mikhailrussell/LAS-Laboratory-Access-System/data/ESP-Now_2_0.01.jpg

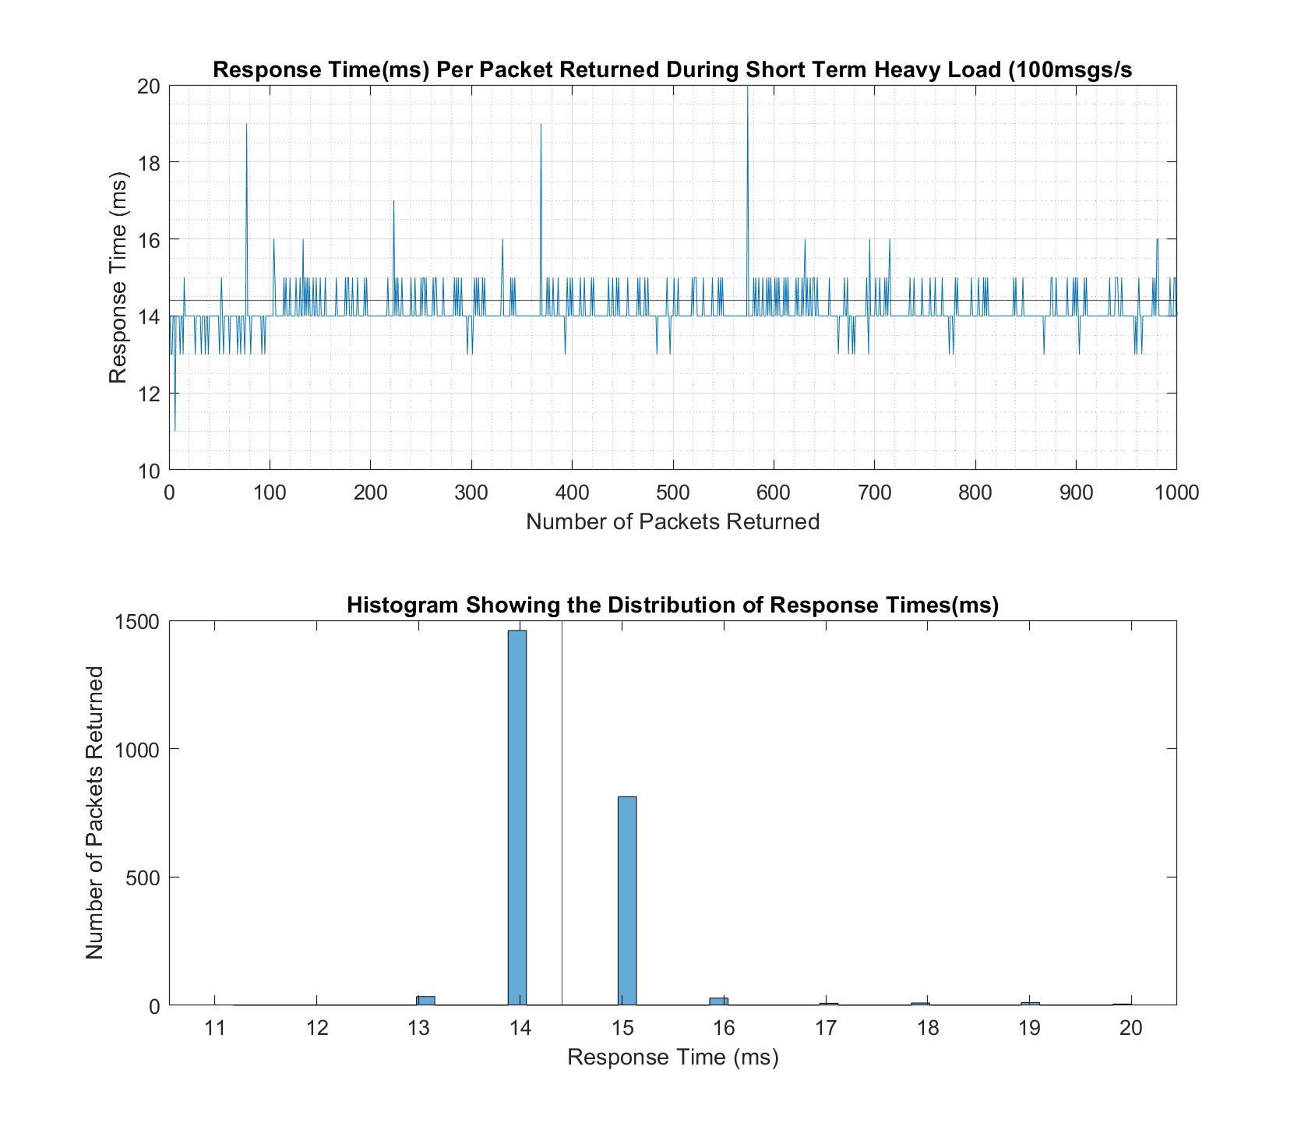
data/ESP-Now_2_0.01.jpg
