mikhailrussell/LAS-Laboratory-Access-System/data/Zero-Crossing_anaylsis/Crossing_image_1.jpg

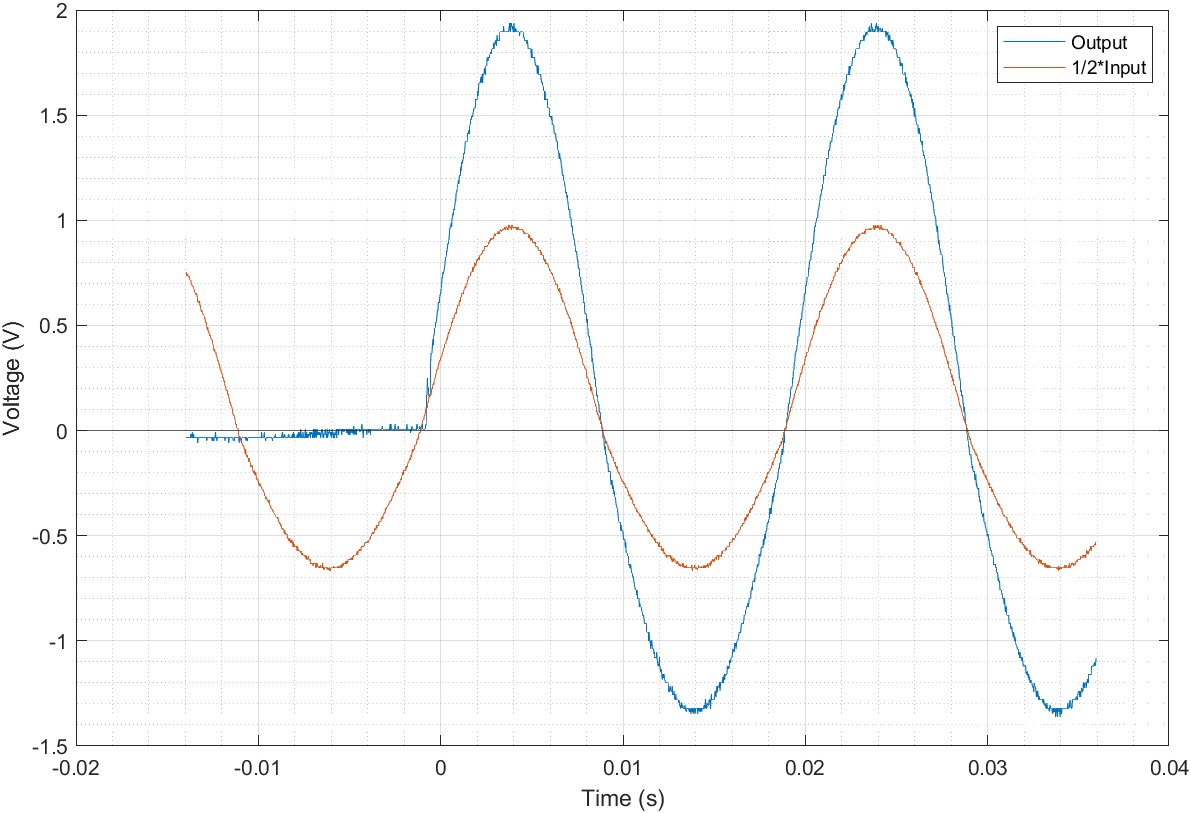
data/Zero-Crossing_anaylsis/Crossing_image_1.jpg
