mikhailrussell/LAS-Laboratory-Access-System/sim/plots/res_sim.png

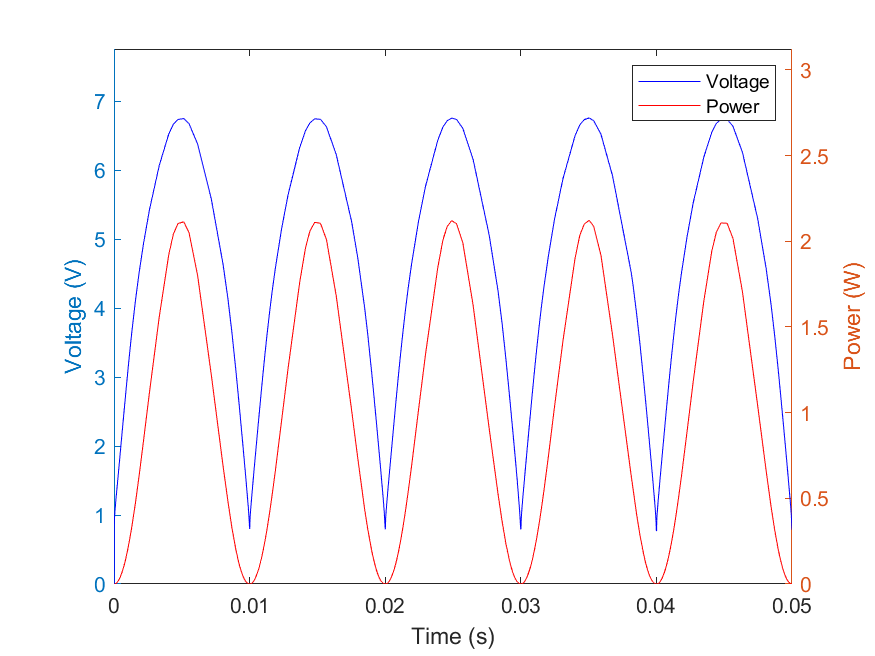
sim/plots/res_sim.png
