mikhailrussell/LAS-Laboratory-Access-System/data/Zero-Crossing_anaylsis/zero_crossing_results.jpg

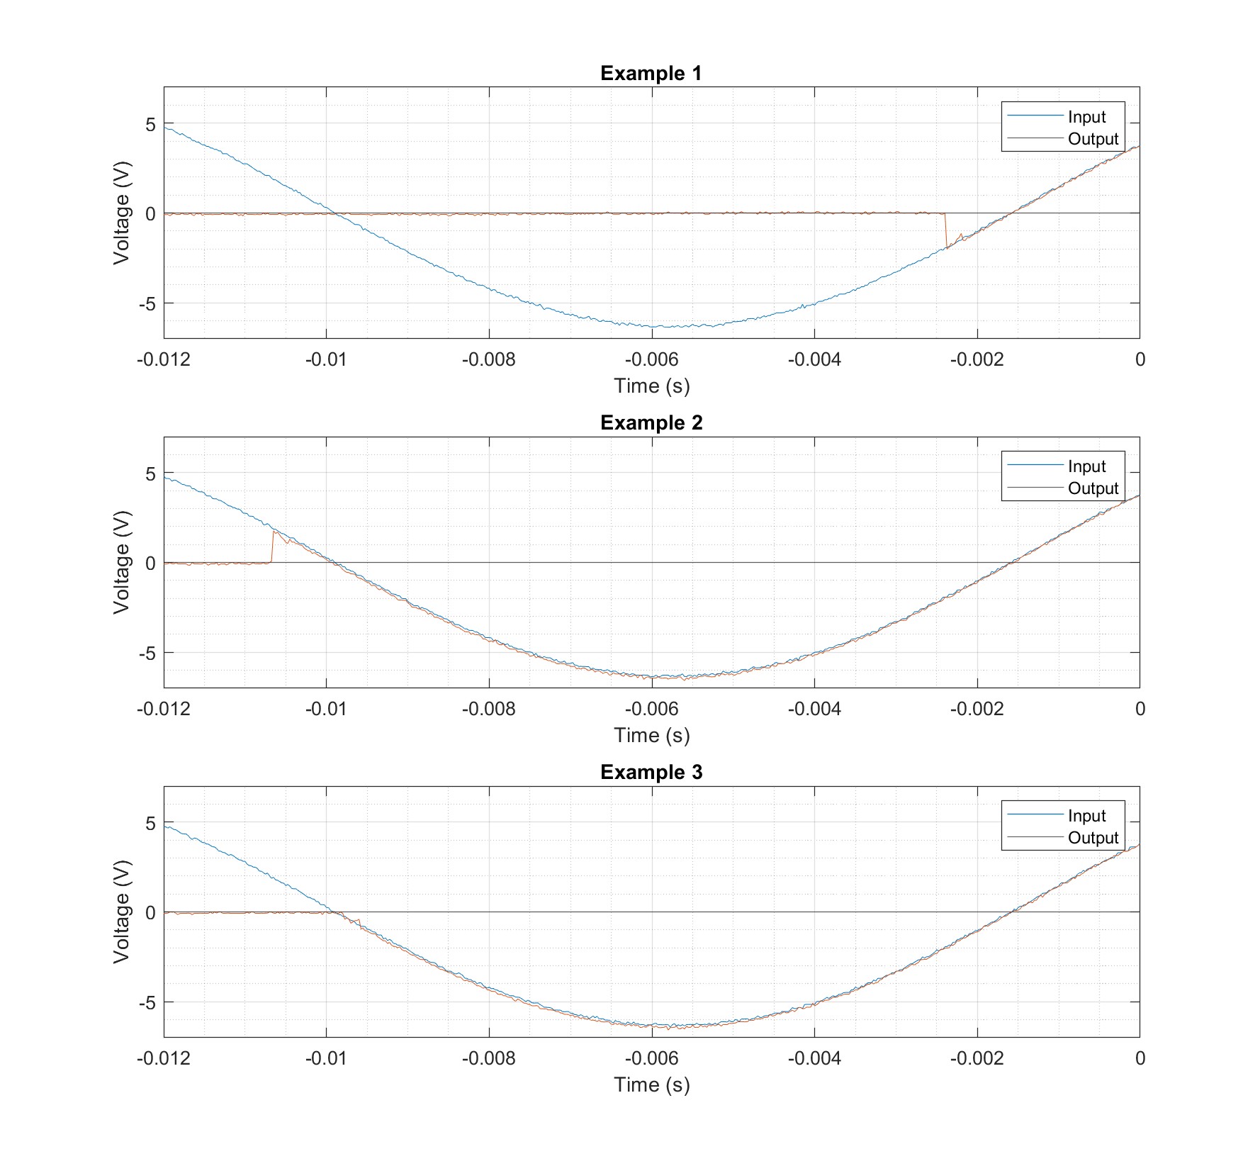
data/Zero-Crossing_anaylsis/zero_crossing_results.jpg
