mikhailrussell/LAS-Laboratory-Access-System/sim/Draft1.asc

D1: diode
D2: diode
D3: diode
D4: diode
R1: res; 100k
R2: res; 100
U2: CNY17-1
V1: voltage; SINE(0 220 60 0.1 0 0)
V3: voltage; 3.3
Named nets: 0, 3.3V
.tran 0 1 0 0.01
