mikhailrussell/LAS-Laboratory-Access-System/sim/relay control.asc

Q1: npn; BC337-25
R1: res; 1.2k
R2: res; 1.2k
R4: res; 1000000
S1: sw; MYSW
V1: voltage; 12
V2: voltage; PULSE(0 3 2 0 0 0.2)
V3: voltage; SINE(0 240 60 0 0 3)
Named nets: 0, +12V, +3V, AC
.tran 10
.model MYSW SW(Ron=1 Roff=1000Meg Vt=.5 Vh=-.4)
