mikhailrussell/LAS-Laboratory-Access-System/sim/ZeroComp.asc

C1: cap; 5p
C2: cap; 330p
D1: zener; UMZ5_1N
D2: diode; 1N4148
D3: diode; 1N4148
D4: diode
D5: diode
D6: diode
D7: diode
Q1: npn; MAT-02
R1: res; 47k
R2: res; 2.2k
R3: res; 1000
R5: res; 7.5k
R6: res; 2700k
R7: res; 4.12k
R8: res; 1000k
R9: res; 4.7k
R10: res; 6.2k
R11: res; 2.2k
U1: LT1017
U2: PC817A
V1: voltage; SINE(0 325 50)
V2: voltage; 3.3
V3: voltage; SINE(0 325 50)
Named nets: 0, 5V, 3.3V
.tran 0 0.05 0 0.01
.incude lm393.lib
.step param n 10 20 10
